Chihhao/esp32_MAX7219_64x16/Arduino_Library/MD_MAX72XX-main/docs/_m_d___m_a_x72xx_8cpp__incl.png

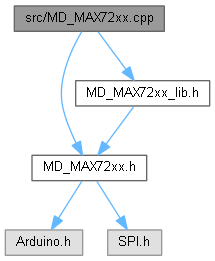
Arduino_Library/MD_MAX72XX-main/docs/_m_d___m_a_x72xx_8cpp__incl.png
