Chihhao/esp32_MAX7219_64x16/Arduino_Library/MD_MAX72XX-main/docs/Generic_conn.jpg

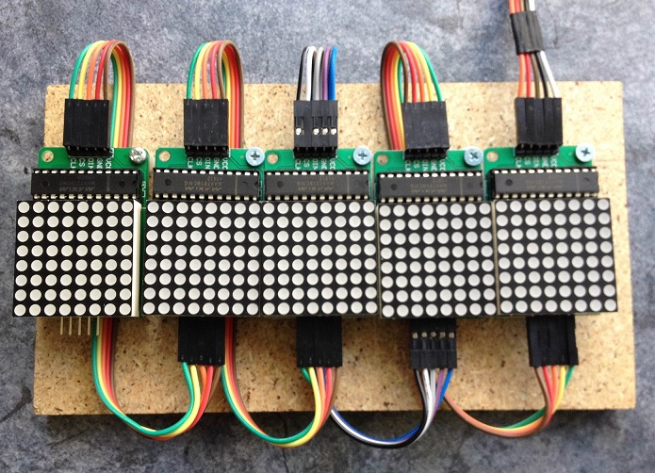
Arduino_Library/MD_MAX72XX-main/docs/Generic_conn.jpg
