Chihhao/esp32_MAX7219_64x16/Arduino_Library/MD_MAX72XX-main/docs/graph_legend.png

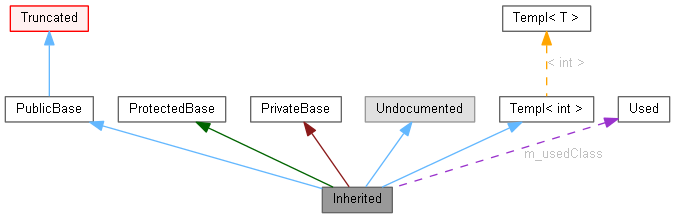
Arduino_Library/MD_MAX72XX-main/docs/graph_legend.png
