Chihhao/esp32_MAX7219_64x16/Arduino_Library/MD_MAX72XX-main/docs/Parola_Module.png

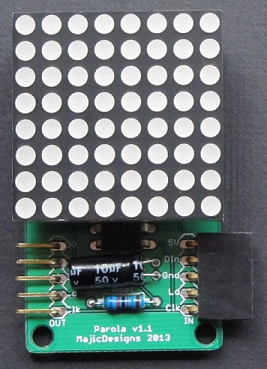
Arduino_Library/MD_MAX72XX-main/docs/Parola_Module.png
