Chihhao/esp32_MAX7219_64x16/Arduino_Library/MD_MAX72XX-main/examples/MD_MAX72xx_RobotEyes/media/photo/RobotEyes_Bare_PCB.JPG

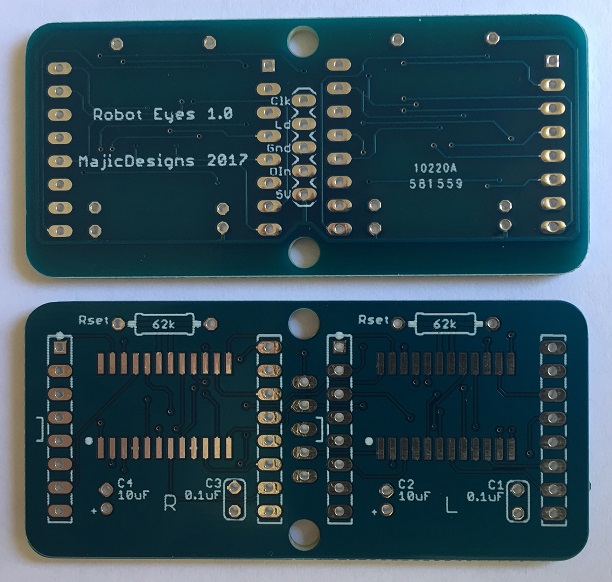
Arduino_Library/MD_MAX72XX-main/examples/MD_MAX72xx_RobotEyes/media/photo/RobotEyes_Bare_PCB.JPG
