Chihhao/esp32_MAX7219_64x16/Arduino_Library/MD_MAX72XX-main/examples/MD_MAX72xx_RobotEyes/media/photo/RobotEyes_Blink0.png

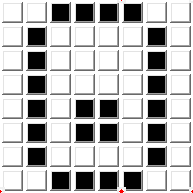
Arduino_Library/MD_MAX72XX-main/examples/MD_MAX72xx_RobotEyes/media/photo/RobotEyes_Blink0.png
