Chihhao/esp32_MAX7219_64x16/Arduino_Library/MD_MAX72XX-main/examples/MD_MAX72xx_RPS_Game/media/RPG Rule.png

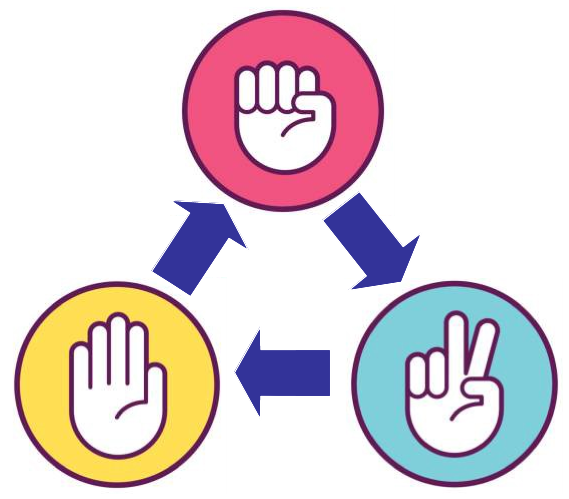
Arduino_Library/MD_MAX72XX-main/examples/MD_MAX72xx_RPS_Game/media/RPG Rule.png
