Chihhao/esp32_MAX7219_64x16/Arduino_Library/MD_MAX72XX-main/media/photo/Controller Top 1.JPG

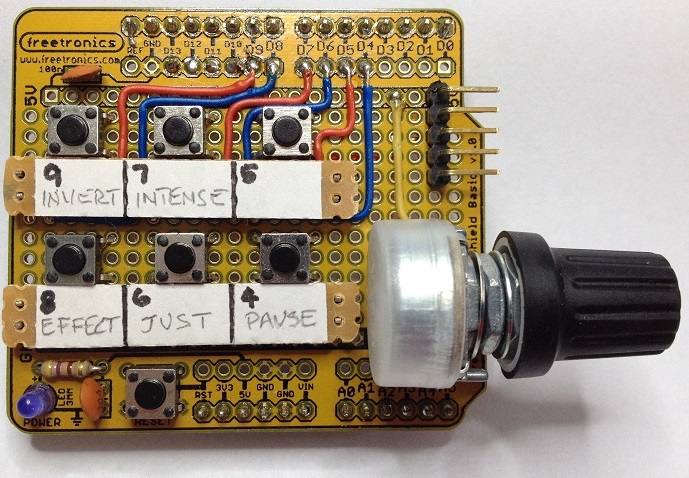
Arduino_Library/MD_MAX72XX-main/media/photo/Controller Top 1.JPG
