Chihhao/esp32_MAX7219_64x16/Arduino_Library/MD_Parola-main/docs/_m_d___parola___h_scroll_8cpp__incl.png

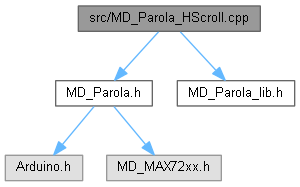
Arduino_Library/MD_Parola-main/docs/_m_d___parola___h_scroll_8cpp__incl.png
