Chihhao/esp32_MAX7219_64x16/Arduino_Library/MD_Parola-main/examples/Parola_Bluetooth_Control/AppInventor/Parola_Control.png

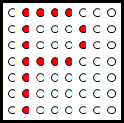
Arduino_Library/MD_Parola-main/examples/Parola_Bluetooth_Control/AppInventor/Parola_Control.png
