Chihhao/esp32_MAX7219_64x16/Arduino_Library/MD_Parola-main/media/photo/Double Height Display/Parola_DH_Hardware_Flip.jpg

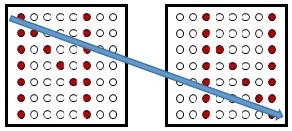
Arduino_Library/MD_Parola-main/media/photo/Double Height Display/Parola_DH_Hardware_Flip.jpg
