Chihhao/esp32_MAX7219_64x16/Arduino_Library/MD_Parola-main/media/photo/Parola_Library.JPG

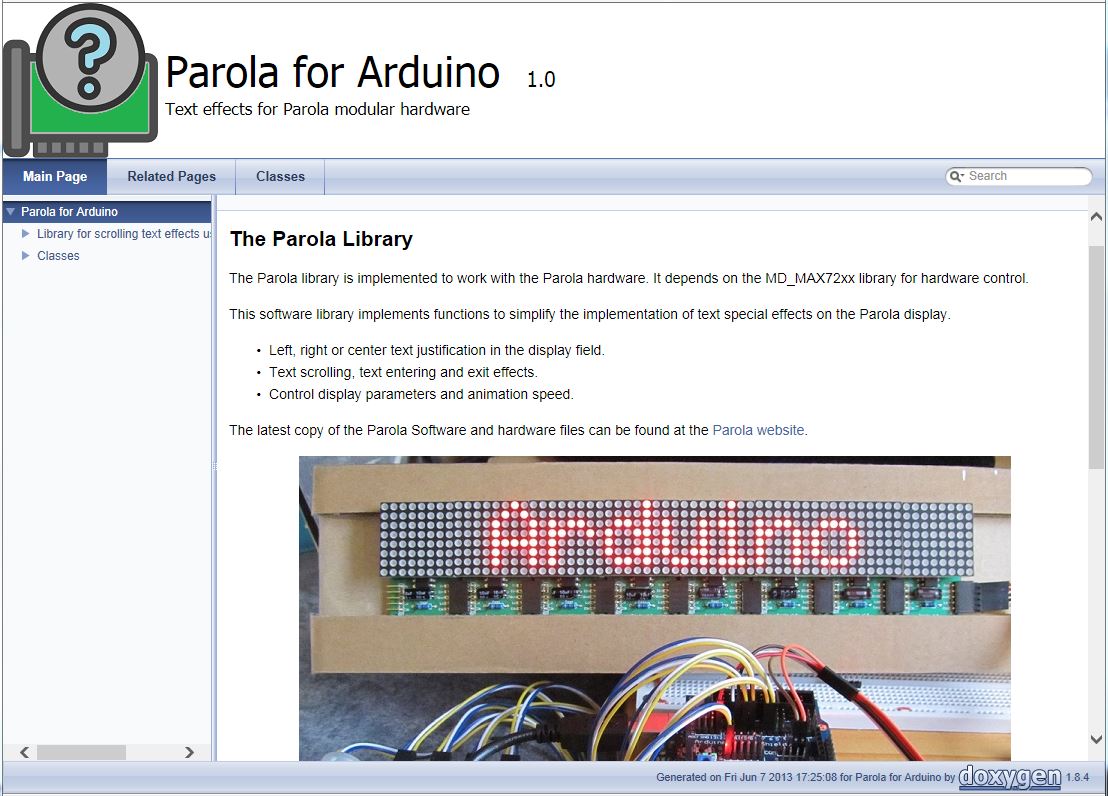
Arduino_Library/MD_Parola-main/media/photo/Parola_Library.JPG
