Chihhao/esp32_MAX7219_64x16/Arduino_Library/MD_Parola-main/media/photo/Sprites/sprite_ghost.png

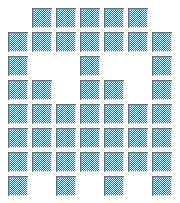
Arduino_Library/MD_Parola-main/media/photo/Sprites/sprite_ghost.png
