Chihhao/esp32_MAX7219_64x16/Arduino_Library/MD_Parola-main/media/photo/Text and Graphics/Text and Graphics.png

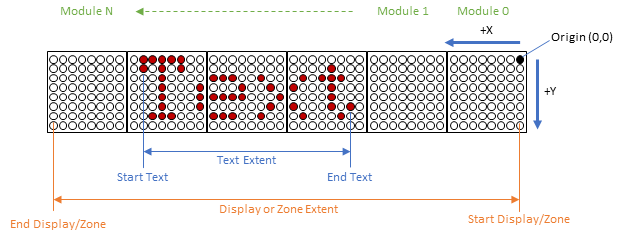
Arduino_Library/MD_Parola-main/media/photo/Text and Graphics/Text and Graphics.png
