Chihhao/esp32_MAX7219_64x16/Images/big-text.png

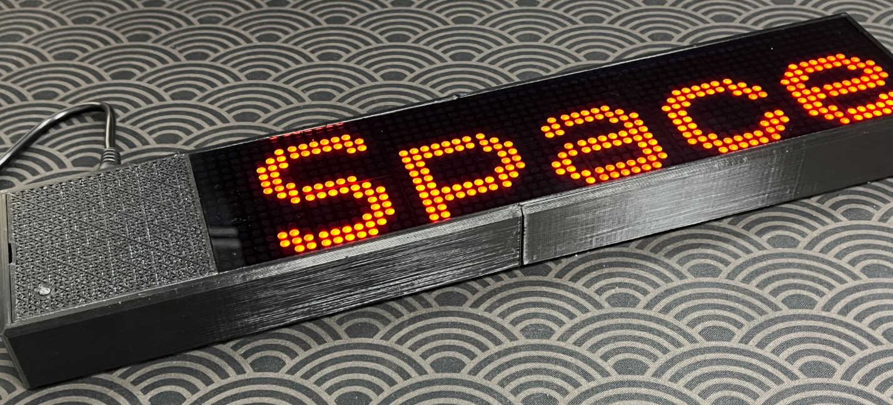
Images/big-text.png
