Chihhao/esp32_MAX7219_64x16/Arduino_Library/MD_Parola-main/media/photo/Assembly/Connector strips.JPG

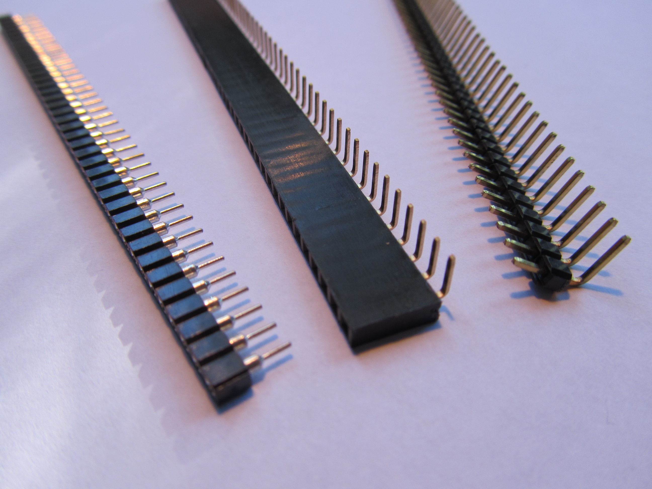
Arduino_Library/MD_Parola-main/media/photo/Assembly/Connector strips.JPG
